patrickslarson8/air_quality_sensor/2022-11-08-14-56-43.png

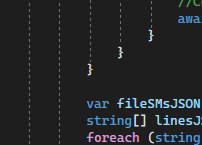
2022-11-08-14-56-43.png
